NOVA-RICS-Open-Lab/open-modular-controller/docs/circuits/LM317Circuit_7V.jpg

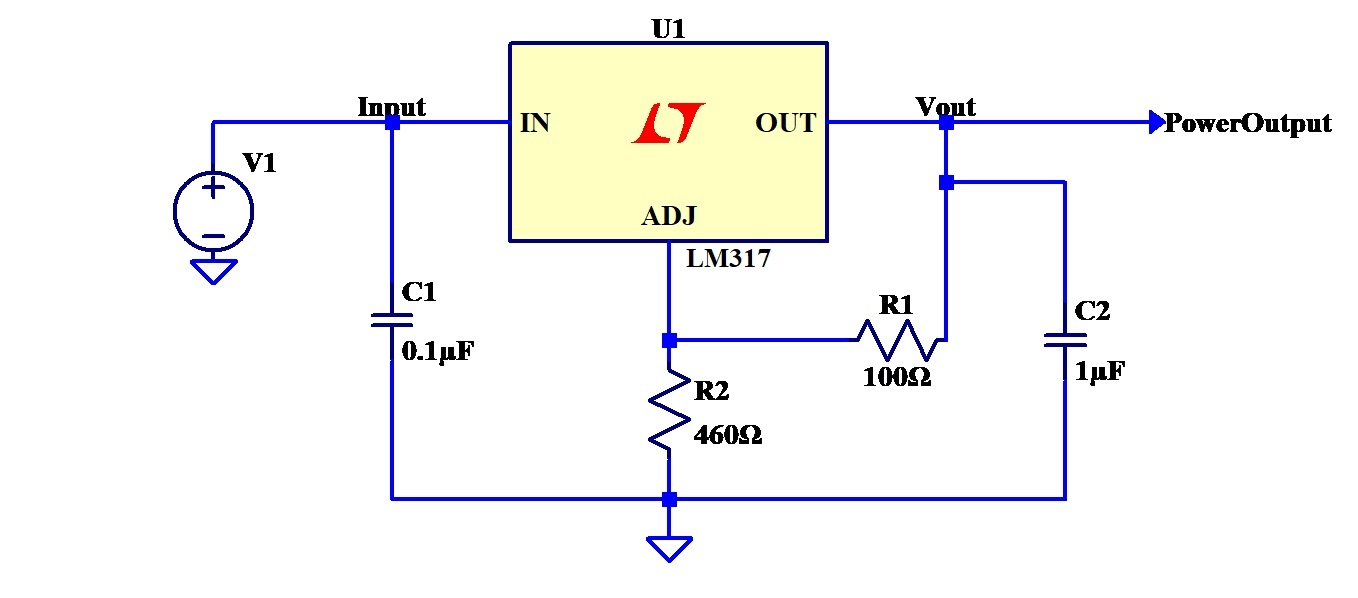
docs/circuits/LM317Circuit_7V.jpg
