NOVA-RICS-Open-Lab/open-modular-controller/imgs/modular_controller_arch.png

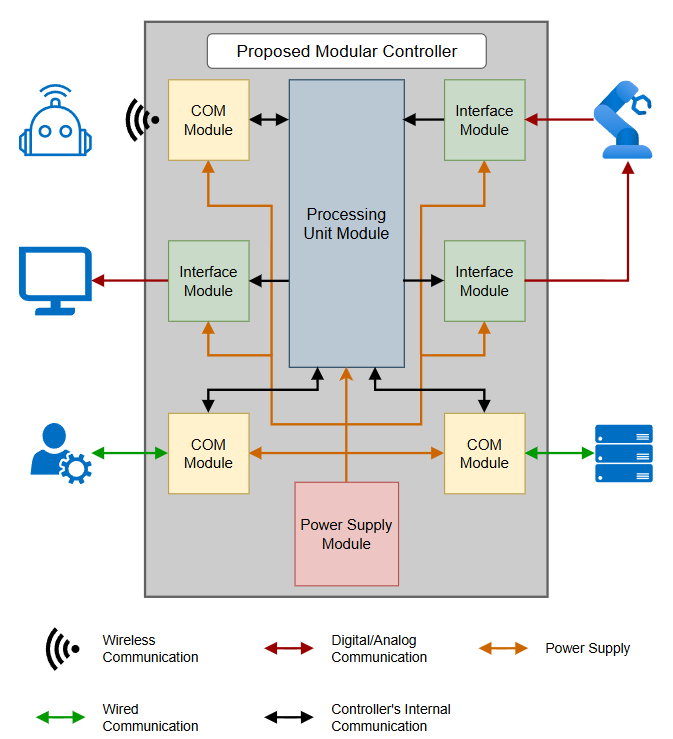
imgs/modular_controller_arch.png
