NOVA-RICS-Open-Lab/open-modular-controller/imgs/pcb_box.jpg

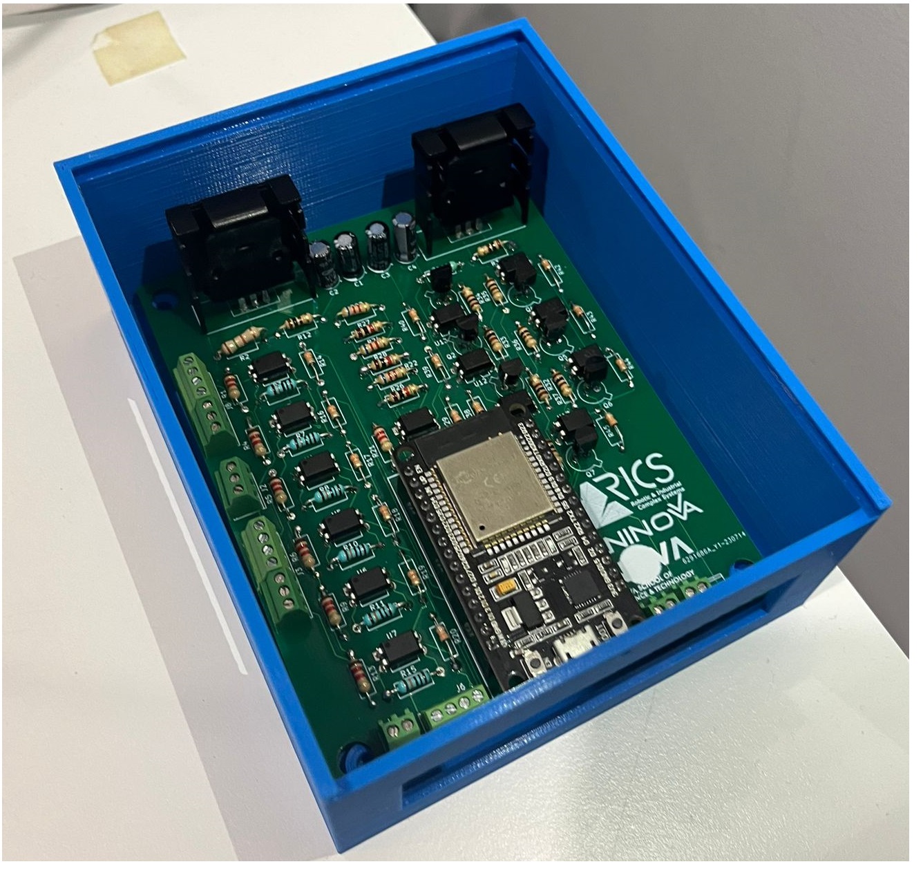
imgs/pcb_box.jpg
