NOVA-RICS-Open-Lab/open-modular-controller/imgs/Protoboard.jpg

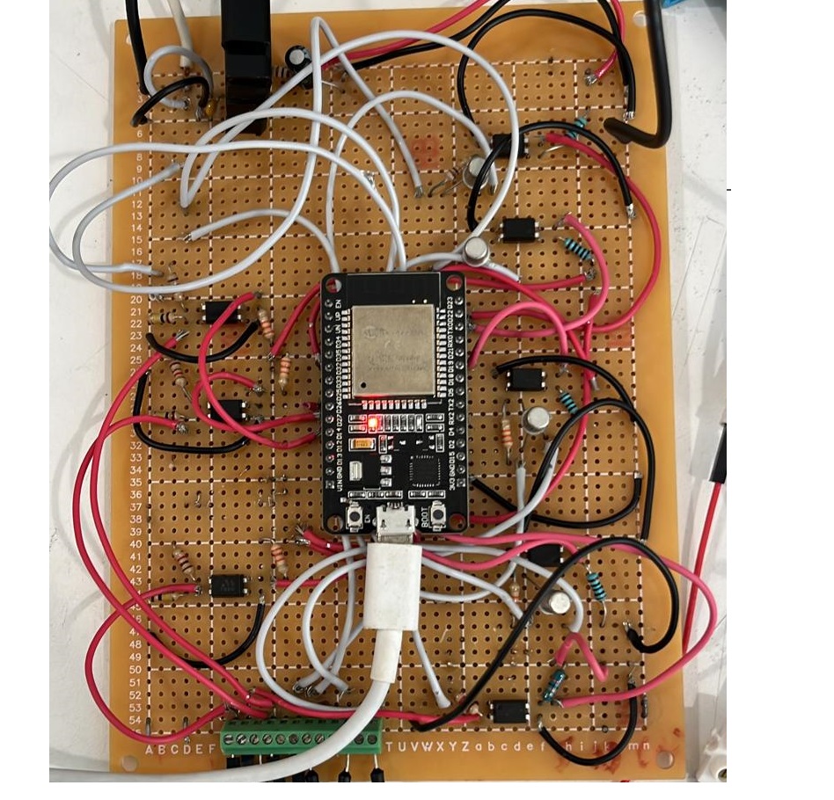
imgs/Protoboard.jpg
