NOVA-RICS-Open-Lab/open-modular-controller/docs/circuits/digital/adjust_tests/33adjusted.jpg

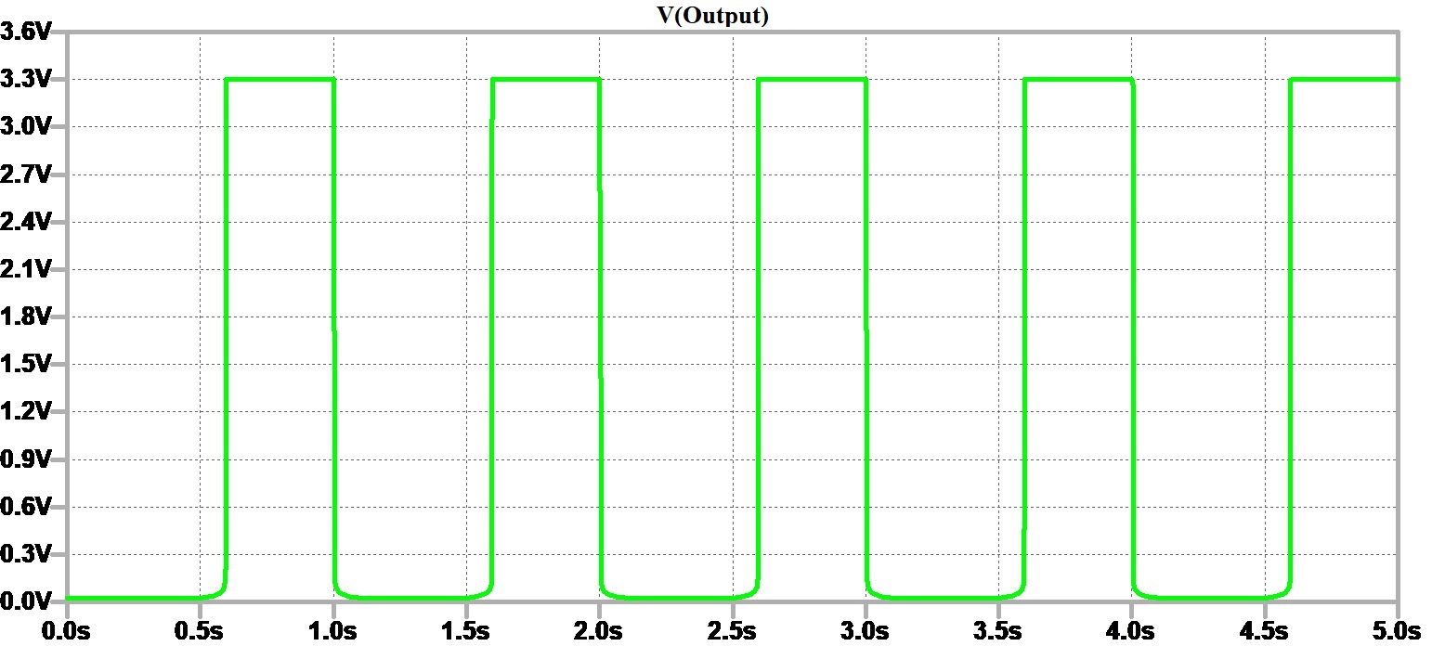
docs/circuits/digital/adjust_tests/33adjusted.jpg
