NOVA-RICS-Open-Lab/open-modular-controller/docs/circuits/digital/adjust_tests/conversion_24-33_adjusted.jpg

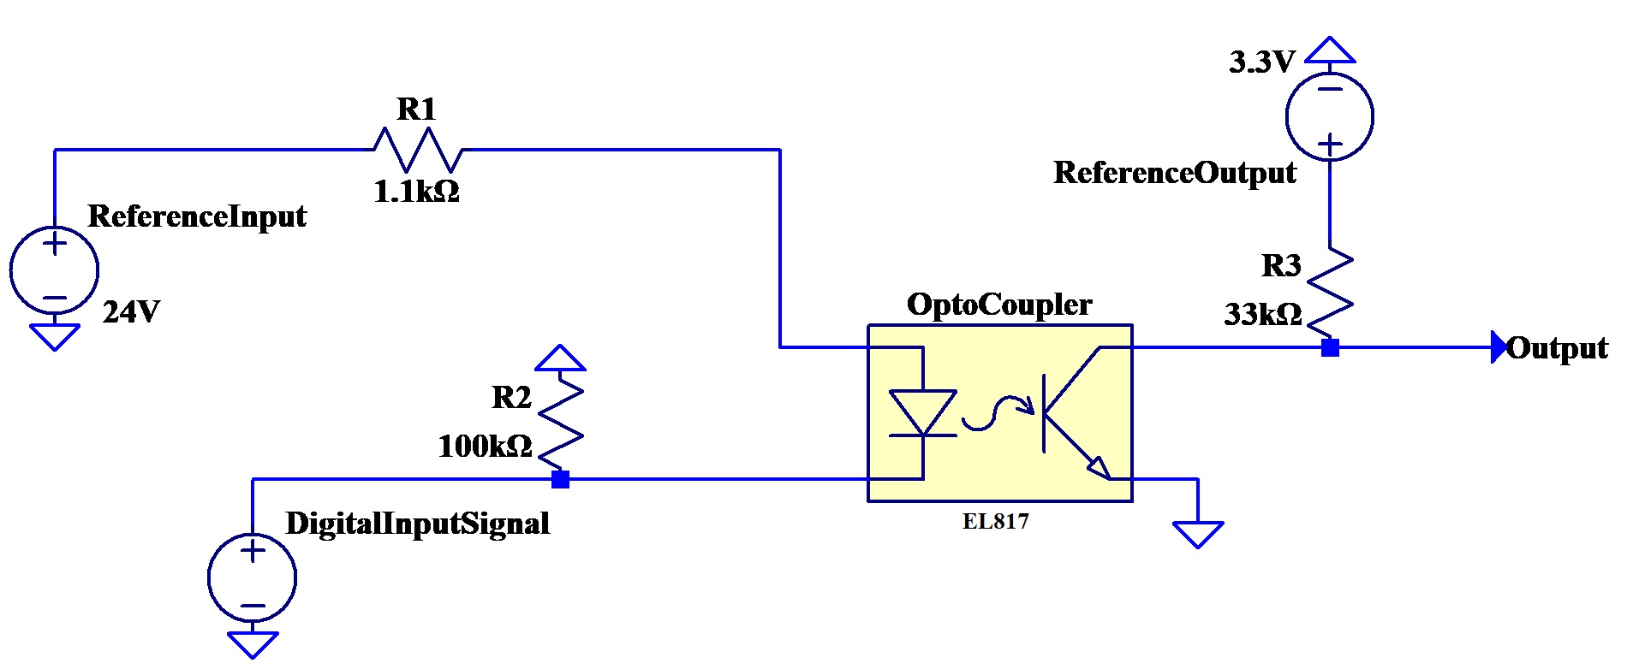
docs/circuits/digital/adjust_tests/conversion_24-33_adjusted.jpg
