NOVA-RICS-Open-Lab/open-modular-controller/docs/circuits/digital/adjust_tests/conversion_33-24_adjusted.jpg

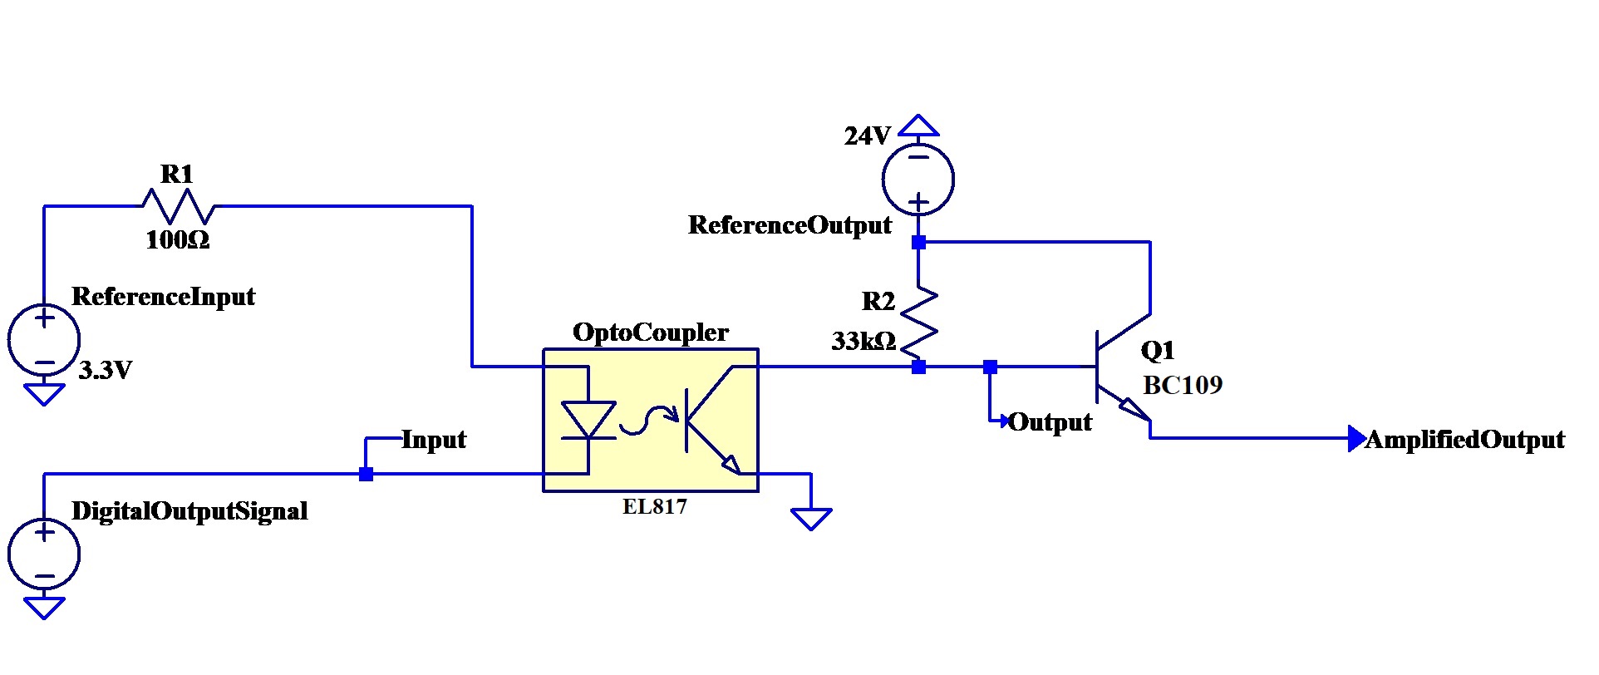
docs/circuits/digital/adjust_tests/conversion_33-24_adjusted.jpg
