NOVA-RICS-Open-Lab/open-modular-controller/docs/circuits/digital/adjust_tests/outputSignal24_T2Update.jpg

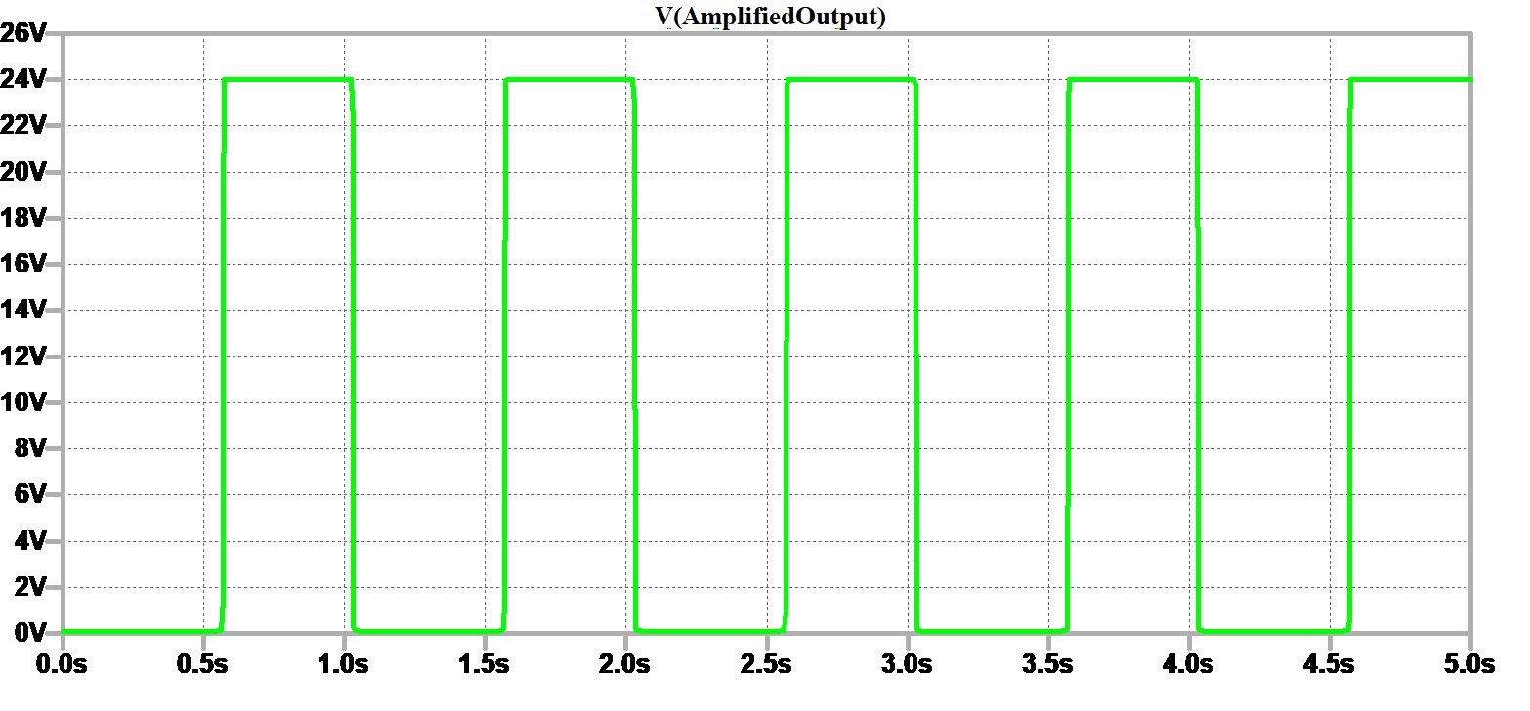
docs/circuits/digital/adjust_tests/outputSignal24_T2Update.jpg
