NOVA-RICS-Open-Lab/open-modular-controller/docs/circuits/digital/Draft1.asc

C1: cap; 0.1µ
C2: cap; 1µ
R1: res; 100
R2: res; 164
U1: LT317A
V1: voltage; 24
Named nets: 0
