NOVA-RICS-Open-Lab/open-modular-controller/docs/pcb/PCB_kicad/PCB.kicad_sch

## KiCad design docs/pcb/PCB_kicad/PCB.kicad_sch (2024-10-26)

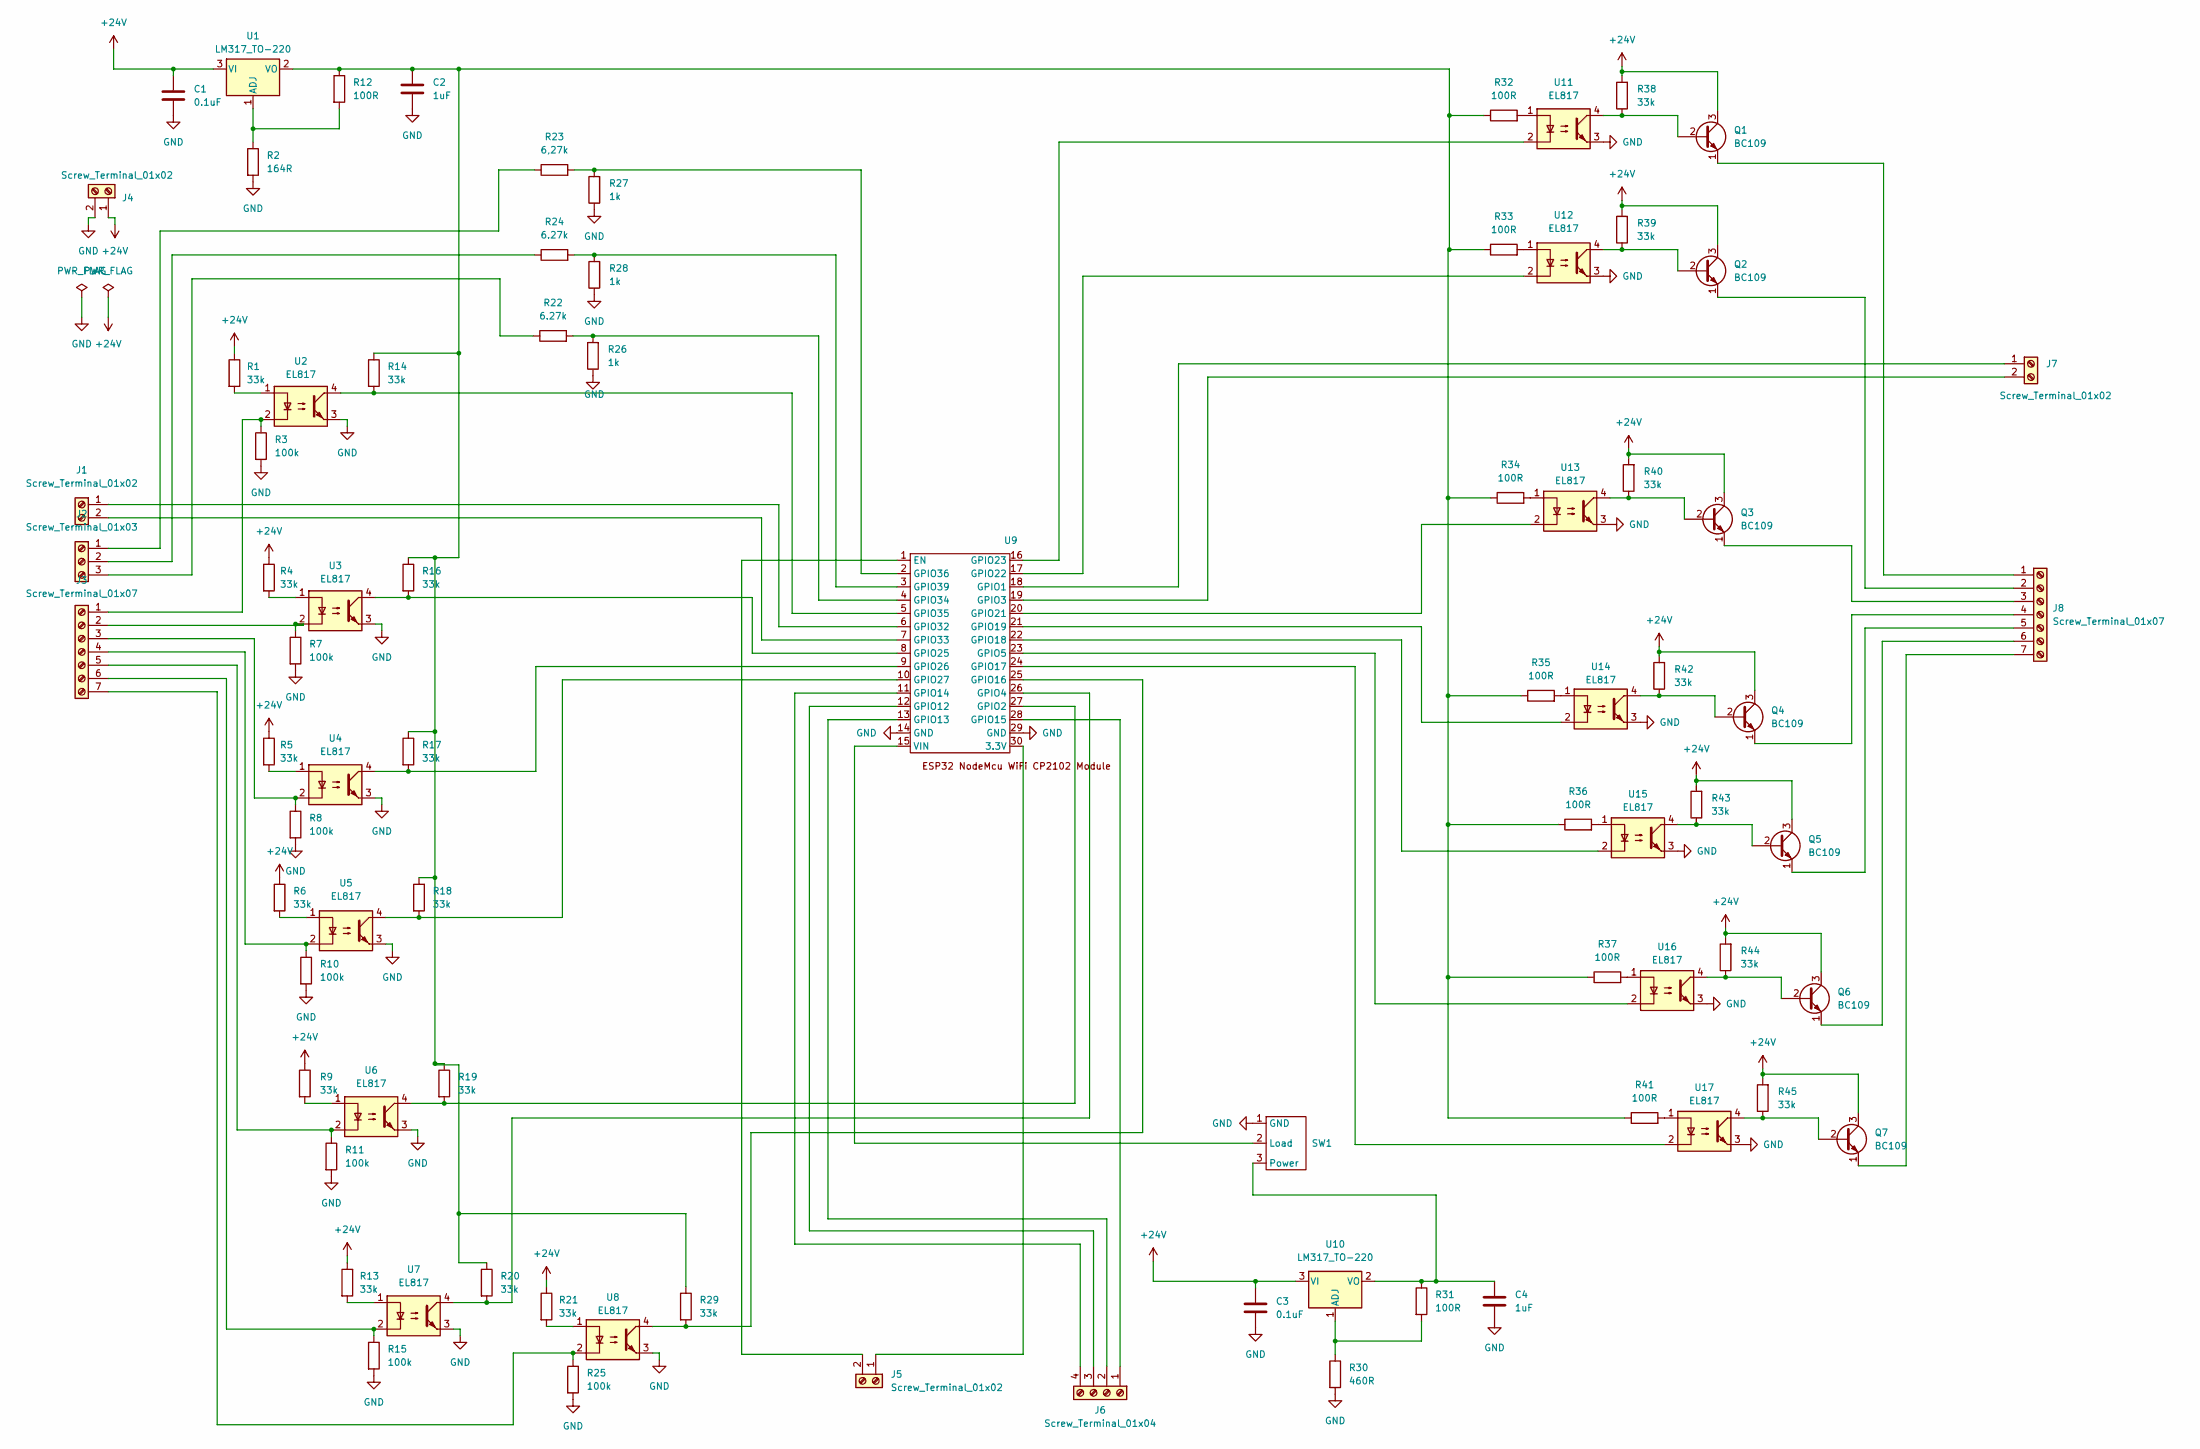
[picture p23: schematic PCB.kicad_sch]

Parts:
C1, C3: 0.1uF; CP_Radial_D5.0mm_P2.00mm
C2, C4: 1uF; CP_Radial_D5.0mm_P2.00mm
J1, J4, J5, J7: Screw_Terminal_01x02; TerminalBlock_Phoenix_MPT-0,5-2-2.54_1x02_P2.54mm_Horizontal
J2: Screw_Terminal_01x03; TerminalBlock_Phoenix_MPT-0,5-3-2.54_1x03_P2.54mm_Horizontal
J3, J8: Screw_Terminal_01x07; TerminalBlock_Phoenix_MPT-0,5-7-2.54_1x07_P2.54mm_Horizontal
J6: Screw_Terminal_01x04; TerminalBlock_Phoenix_MPT-0,5-4-2.54_1x04_P2.54mm_Horizontal
Q1, Q2, Q3, Q4, Q5, Q6, Q7: BC109; TO-18-3
R1, R4, R5, R6, R9, R13, R14, R16, R17, R18, R19, R20, R21, R29, R38, R39, R40, R42, R43, R44, R45: 33k; R_Axial_DIN0207_L6.3mm_D2.5mm_P10.16mm_Horizontal
R2: 164R; R_Axial_DIN0207_L6.3mm_D2.5mm_P10.16mm_Horizontal
R3, R7, R8, R10, R11, R15, R25: 100k; R_Axial_DIN0207_L6.3mm_D2.5mm_P10.16mm_Horizontal
R12, R31, R32, R33, R34, R35, R36, R37, R41: 100R; R_Axial_DIN0207_L6.3mm_D2.5mm_P10.16mm_Horizontal
R22, R24: 6.27k; R_Axial_DIN0207_L6.3mm_D2.5mm_P10.16mm_Horizontal
R23: 6,27k; R_Axial_DIN0207_L6.3mm_D2.5mm_P10.16mm_Horizontal
R26, R27, R28: 1k; R_Axial_DIN0207_L6.3mm_D2.5mm_P10.16mm_Horizontal
R30: 460R; R_Axial_DIN0207_L6.3mm_D2.5mm_P10.16mm_Horizontal
SW1: Switch
U1, U10: LM317_TO-220; TO-220-3_Vertical
U2, U3, U4, U5, U6, U7, U8, U11, U12, U13, U14, U15, U16, U17: EL817; DIP-4_W7.62mm
U9: ESP32-JOYIT

Connections:
+24V: C1.1, C3.1, J4.1, Q1.3 (C), Q2.3 (C), Q3.3 (C), Q4.3 (C), Q5.3 (C), Q6.3 (C), Q7.3 (C), R1.1, R4.1, R5.1, R6.1, R9.1, R13.1, R21.1, R38.2, R39.2, R40.2, R42.2, R43.2, R44.2, R45.2, U1.3 (VI), U10.3 (VI)
GND: C1.2, C2.2, C3.2, C4.2, J4.2, R2.2, R3.2, R7.2, R8.2, R10.2, R11.2, R15.2, R25.2, R26.1, R27.1, R28.1, R30.2, SW1.1 (GND), U2.3, U3.3, U4.3, U5.3, U6.3, U7.3, U8.3, U9.14 (GND), U9.29 (GND), U11.3, U12.3, U13.3, U14.3, U15.3, U16.3, U17.3
unnamed: C2.1, R12.1, R14.1, R16.1, R17.1, R18.1, R19.1, R20.1, R29.1, R32.1, R33.1, R34.1, R35.1, R36.1, R37.1, R41.1, U1.2 (VO)
unnamed: C4.1, R31.1, SW1.3 (Power), U10.2 (VO)
unnamed: J1.1, U9.6 (GPIO32)
unnamed: J1.2, U9.7 (GPIO33)
unnamed: J2.1, R23.1
unnamed: J2.2, R24.1
unnamed: J2.3, R22.1
unnamed: J3.1, R3.1, U2.2
unnamed: J3.2, R7.1, U3.2
unnamed: J3.3, R8.1, U4.2
unnamed: J3.4, R10.1, U5.2
unnamed: J3.5, R11.1, U6.2
unnamed: J3.6, R15.1, U7.2
unnamed: J3.7, R25.1, U8.2
unnamed: J5.1, U9.30 (3.3V)
unnamed: J5.2, U9.1 (EN)
unnamed: J6.1, U9.28 (GPIO15)
unnamed: J6.2, U9.13 (GPIO13)
unnamed: J6.3, U9.12 (GPIO12)
unnamed: J6.4, U9.11 (GPIO14)
unnamed: J7.1, U9.18 (GPIO1)
unnamed: J7.2, U9.19 (GPIO3)
unnamed: J8.1, Q1.1 (E)
unnamed: J8.2, Q2.1 (E)
unnamed: J8.3, Q3.1 (E)
unnamed: J8.4, Q4.1 (E)
unnamed: J8.5, Q5.1 (E)
unnamed: J8.6, Q6.1 (E)
unnamed: J8.7, Q7.1 (E)
unnamed: Q1.2 (B), R38.1, U11.4
unnamed: Q2.2 (B), R39.1, U12.4
unnamed: Q3.2 (B), R40.1, U13.4
unnamed: Q4.2 (B), R42.1, U14.4
unnamed: Q5.2 (B), R43.1, U15.4
unnamed: Q6.2 (B), R44.1, U16.4
unnamed: Q7.2 (B), R45.1, U17.4
unnamed: R1.2, U2.1
unnamed: R4.2, U3.1
unnamed: R5.2, U4.1
unnamed: R6.2, U5.1
unnamed: R9.2, U6.1
unnamed: R2.1, R12.2, U1.1 (ADJ)
unnamed: R13.2, U7.1
unnamed: R14.2, U2.4, U9.5 (GPIO35)
unnamed: R16.2, U3.4, U9.8 (GPIO25)
unnamed: R17.2, U4.4, U9.9 (GPIO26)
unnamed: R18.2, U5.4, U9.10 (GPIO27)
unnamed: R19.2, U6.4, U9.27 (GPIO2)
unnamed: R20.2, U7.4, U9.26 (GPIO4)
unnamed: R21.2, U8.1
unnamed: R22.2, R26.2, U9.4 (GPIO34)
unnamed: R23.2, R27.2, U9.2 (GPIO36)
unnamed: R24.2, R28.2, U9.3 (GPIO39)
unnamed: R29.2, U8.4, U9.25 (GPIO16)
unnamed: R30.1, R31.2, U10.1 (ADJ)
unnamed: R32.2, U11.1
unnamed: R33.2, U12.1
unnamed: R34.2, U13.1
unnamed: R35.2, U14.1
unnamed: R36.2, U15.1
unnamed: R37.2, U16.1
unnamed: R41.2, U17.1
unnamed: SW1.2 (Load), U9.15 (VIN)
unnamed: U9.16 (GPIO23), U11.2
unnamed: U9.17 (GPIO22), U12.2
unnamed: U9.20 (GPIO21), U13.2
unnamed: U9.21 (GPIO19), U14.2
unnamed: U9.22 (GPIO18), U15.2
unnamed: U9.23 (GPIO5), U16.2
unnamed: U9.24 (GPIO17), U17.2
